shibayan1122/PWS/software/pws_manager/pws_manager.h

///////////////////////////////////////////////////////////
// pws_manager.h
///////////////////////////////////////////////////////////
#ifndef __PWS_MANAGER_H__
#define __PWS_MANAGER_H__

#include "def.h"

//
//  内部通信メッセージ
//
#define MSG_INITIALIZE          "/system/initialize"            // 初期化要求
#define MSG_SHUTDOWN            "/system/shutdown"              // シャットダウン要求
#define MSG_PUSH_AP_SET_BTN     "/btnmonitor/push/apset"        // AP設定ボタン押下
#define MSG_PUSH_REC_BTN        "/btnmonitor/push/recbtn"       // 録音ボタン押下
#define MSG_PUSH_PLAY_BTN       "/btnmonitor/push/playbtn"      // 再生ボタン押下
#define MSG_PUSH_VOL_UP_BTN     "/btnmonitor/push/volupbtn"     // ボリュームアップボタン押下
#define MSG_PUSH_VOL_DOWN_BTN   "/btnmonitor/push/voldownbtn"   // ボリュームダウンボタン押下
#define MSG_PUSH_EFFECT_BTN     "/btnmonitor/push/effectbtn"    // エフェクトボタン押下
#define MSG_PUSH_TUNING_BTN     "/btnmonitor/push/tuningbtn"    // チューニングボタン押下
#define MSG_PUSH_SHUTDOWN_BTN   "/btnmonitor/push/shutdownbtn"  // シャットダウンボタン押下

#endif // __PWS_MANAGER_H__
